mandelllee/TheProfessorV2/pcb/Leaflift_core_v1_PCB1_854134560_etch_silk_bottom.pdf

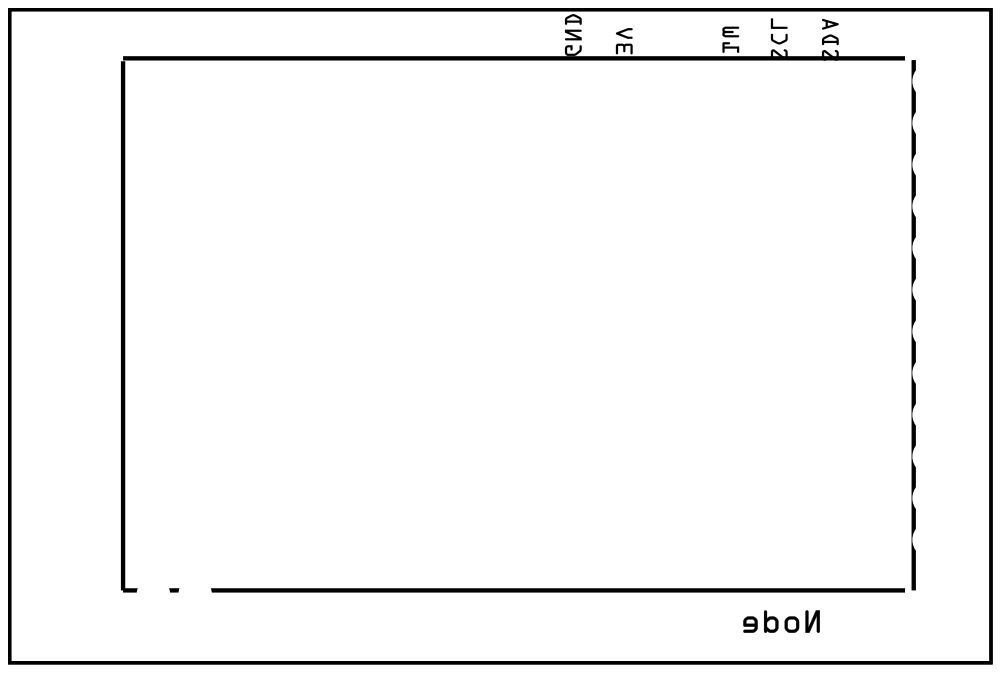
[picture p9: page 1]
