mandelllee/TheProfessorV2/pcb/Leaflift_core_v1_PCB1_854134560_etch_silk_top_mirror.pdf

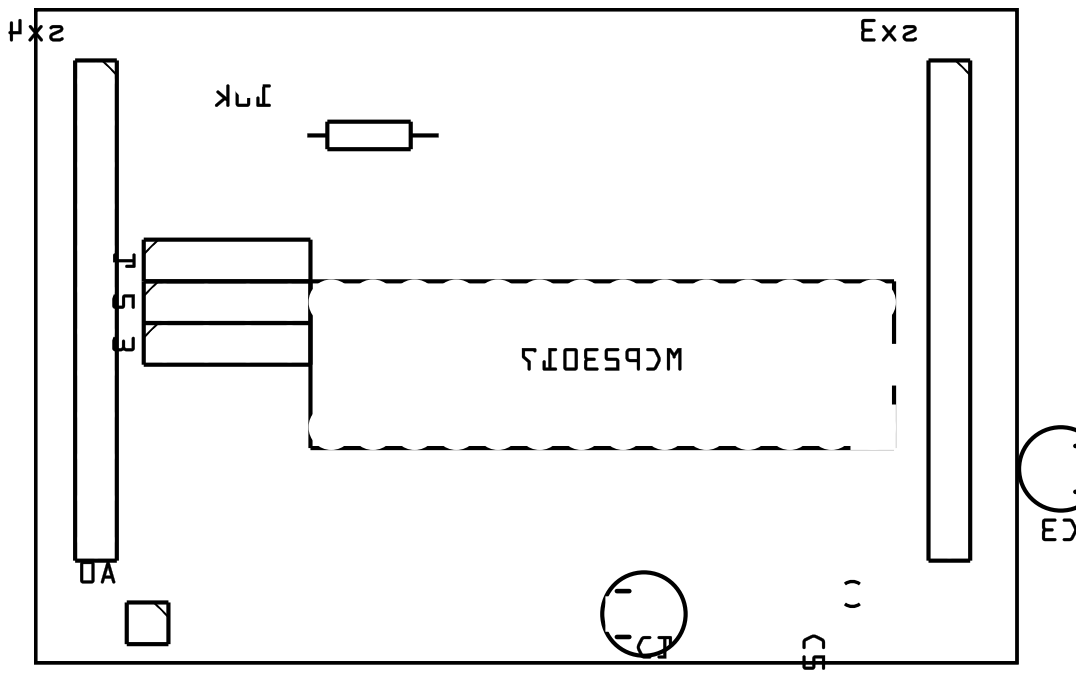
[picture p12: page 1]
