mandelllee/TheProfessorV2/sketches/LeafLift_core/leaflift_images.h

// TOOL for creating PROGMEM images
//http://javl.github.io/image2cpp/

const unsigned char otaIcon [] PROGMEM = {
  0xff, 0xff, 0xff, 0xff, 0x80, 0x00, 0x00, 0x01, 0x80, 0x00, 0x00, 0x01, 0x87, 0xef, 0xf3, 0x81,
  0x8e, 0x73, 0x83, 0x81, 0x8e, 0x73, 0x87, 0xc1, 0x8e, 0x73, 0x87, 0xe1, 0x8e, 0x73, 0x87, 0xe1,
  0x8e, 0x73, 0x8e, 0x71, 0x8e, 0x73, 0x8e, 0x71, 0x8e, 0x73, 0x8f, 0xf1, 0x8e, 0x73, 0x8f, 0xf1,
  0x8e, 0x73, 0x8e, 0x71, 0x87, 0xe3, 0x8e, 0x71, 0x80, 0x00, 0x00, 0x01, 0xff, 0xff, 0xff, 0xff,

};

const unsigned char bluetoothIcon [] PROGMEM = {
  0x00, 0x00, 0x01, 0x00, 0x01, 0x80, 0x01, 0xe0, 0x01, 0xb0, 0x0d, 0xb0, 0x07, 0xe0, 0x03, 0x80,
  0x03, 0x80, 0x07, 0xe0, 0x0d, 0xb0, 0x01, 0xb0, 0x01, 0xc0, 0x01, 0x80, 0x01, 0x00, 0x00, 0x00,

};
const unsigned char launchScreen [] PROGMEM = {
  0x00, 0x00, 0x00, 0x00, 0x00, 0x00, 0x00, 0x00, 0x00, 0x00, 0x00, 0x00, 0x00, 0x00, 0x00, 0x00,
  0x00, 0x00, 0x00, 0x00, 0x00, 0x00, 0x00, 0x00, 0x00, 0x00, 0x00, 0x00, 0x00, 0x00, 0x00, 0x00,
  0x00, 0x00, 0x00, 0x00, 0x00, 0x00, 0x00, 0x00, 0x00, 0x00, 0x00, 0x00, 0x00, 0x00, 0x00, 0x00,
  0x00, 0x00, 0x00, 0x00, 0x00, 0x00, 0x00, 0x00, 0x00, 0x00, 0x00, 0x00, 0x00, 0x00, 0x00, 0x00,
  0x00, 0x00, 0x00, 0x0f, 0x00, 0x00, 0x00, 0x00, 0x00, 0x00, 0x00, 0x00, 0x00, 0x00, 0x00, 0x00,
  0x00, 0x00, 0x00, 0x7f, 0x80, 0x00, 0x00, 0x00, 0x00, 0x00, 0x00, 0x00, 0x00, 0x00, 0x00, 0x00,
  0x00, 0x00, 0x01, 0xff, 0xc0, 0x00, 0x00, 0x00, 0x00, 0x00, 0x00, 0x00, 0x00, 0x00, 0x00, 0x00,
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
  0x00, 0x00, 0x00, 0x00, 0x00, 0x1f, 0xe0, 0x00, 0x00, 0x00, 0x00, 0x00, 0x0f, 0x00, 0x00, 0x00,
  0x00, 0x00, 0x00, 0x00, 0x00, 0x1f, 0x80, 0x00, 0x00, 0x00, 0x06, 0x00, 0x0f, 0x00, 0x00, 0x00,
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

};
